sergeantd83/OT-Thing/Firmware/src/portal.cpp

#include <WiFi.h>
#include <Update.h>
#include <ArduinoJson.h>
#include <AsyncTCP.h>
#include <ESPAsyncWebServer.h>
#include <WiFi.h>
#include "portal.h"
#include "devstatus.h"
#include "devconfig.h"
#include "html.h"
#include "otcontrol.h"
#include "otvalues.h"
#include "httpUpdate.h"

static const char APP_JSON[] PROGMEM = "application/json";
#ifdef NODO
const IPAddress apAddress(4, 3, 2, 1);
const IPAddress apMask(255, 255, 255, 0);
#else
static const IPAddress apAddress(4, 3, 2, 1);
static const IPAddress apMask(255, 255, 255, 0);
#endif
Portal portal;
static AsyncWebServer websrv(80);
AsyncWebSocket ws("/ws");


Portal::Portal():
    reboot(false),
    updateEnable(true) {
}

void Portal::begin(bool configMode) {
    if (configMode) {
        WiFi.persistent(false);
#ifdef NODO
        WiFi.disconnect();
        WiFi.mode(WIFI_AP);   // Force AP only so DHCP works reliably
#endif
        WiFi.softAPConfig(apAddress, apAddress, apMask);
#ifdef NODO
        delay(200); // allow stack to settle
        if (!WiFi.softAP(F(AP_SSID), F(AP_PASSWORD))) 
            Serial.println("Failed to start AP"); // print message if setup fails
        else
            Serial.println("AP started successfully");
#else
        WiFi.softAP(F(AP_SSID), F(AP_PASSWORD));

        if (WiFi.SSID().isEmpty())
            WiFi.mode(WIFI_AP);
        else
            WiFi.mode(WIFI_AP_STA);
#endif
        WiFi.setAutoReconnect(false);
#ifndef NODO
        WiFi.persistent(true);
#endif
    }

    websrv.begin();
    websrv.addHandler(&ws);

    websrv.on("/", HTTP_ANY, [](AsyncWebServerRequest *request) {
        #ifdef DEBUG
        if (LittleFS.exists(F("/index.html"))) {
            request->send(LittleFS, F("/index.html"), F("text/html"));
            return;
        }
        #endif
        request->send(200, F("text/html"), (uint8_t*) html, strlen_P(html));
    });

    websrv.on(PSTR("/config"), HTTP_GET, [this] (AsyncWebServerRequest *request) {
        if (LittleFS.exists(FPSTR(CFG_FILENAME)))
            request->send(LittleFS, FPSTR(CFG_FILENAME), FPSTR(APP_JSON));
        else
            request->send(404);
    });

    websrv.on(PSTR("/config"), HTTP_POST, 
        [this] (AsyncWebServerRequest *request) {
        },
        [] (AsyncWebServerRequest *request, const String &filename, size_t index, uint8_t *data, size_t len, bool final) {
        },
        [this] (AsyncWebServerRequest *request, uint8_t *data, size_t len, size_t index, size_t total) {
            static String confBuf;
            if (!index)
                confBuf.clear();

            confBuf.concat((const char*) data, len);

            if (confBuf.length() == total) {
                devconfig.write(confBuf);
                confBuf.clear();
                request->send(200);
            }
        }
    );

    websrv.on(PSTR("/scan"), HTTP_GET, [this] (AsyncWebServerRequest *request) {
        JsonDocument doc;
        JsonObject jobj = doc.to<JsonObject>();

        int n = WiFi.scanComplete();
        jobj[F("status")] = n;
        if (n == -2)
            WiFi.scanNetworks(true);
        else
            if (n >= 0) {
                JsonArray results = jobj[F("results")].to<JsonArray>();
                for (int i=0; i<n; i++) {
                    JsonObject result = results.add<JsonObject>();
                    result[F("ssid")] = WiFi.SSID(i);
                    result[F("rssi")] = WiFi.RSSI(i);
                    result[F("channel")] = WiFi.channel(i);
                }
                WiFi.scanDelete();
            }

        AsyncResponseStream *response = request->beginResponseStream(FPSTR(APP_JSON));
        serializeJson(doc, *response);
        request->send(response);
    });

    websrv.on(PSTR("/setwifi"), HTTP_POST, [this] (AsyncWebServerRequest *request) {
        if (request->hasArg(F("ssid")) && request->hasArg(F("pass"))) {
#ifndef NODO
            request->send(200);
            delay(500);
#endif
            WiFi.disconnect();
            WiFi.persistent(true);
            WiFi.setAutoReconnect(true);
            String ssid = request->arg(F("ssid"));
            String pass = request->arg(F("pass"));
            WiFi.begin(ssid, pass);
#ifdef NODO
            // Trigger the reboot flag handled in Portal::loop()
            this->reboot = true;
            request->send(200, "text/plain", "Credentials Saved. Rebooting...");
#endif
        }
        else
            request->send(400); // bad request
    });

    websrv.on(PSTR("/status"), HTTP_GET, [this](AsyncWebServerRequest *request) {
        if (httpupdate.isUpdating()) {
            request->send(503);
            return;
        }
        JsonDocument doc;
        devstatus.buildDoc(doc);
        AsyncResponseStream *response = request->beginResponseStream(FPSTR(APP_JSON));
        serializeJson(doc, *response);
        request->send(response);
    });

    websrv.on(PSTR("/otitems"), HTTP_GET, [this](AsyncWebServerRequest *request) {
        if (httpupdate.isUpdating()) {
            request->send(503);
            return;
        }
        JsonDocument doc;
        JsonObject jSlave = doc[F("slave")].to<JsonObject>();
            for (auto *valobj: slaveValues)
                valobj->getStatus(jSlave);

        JsonObject jMaster = doc[F("master")].to<JsonObject>();
            for (auto *valobj: thermostatValues)
                valobj->getStatus(jMaster);

        AsyncResponseStream *response = request->beginResponseStream(FPSTR(APP_JSON));
        serializeJson(doc, *response);
        request->send(response);
    });

    websrv.on(PSTR("/reboot"), HTTP_GET, [this](AsyncWebServerRequest *request) {
        request->send(200);
        this->reboot = true;
    });

    websrv.on(PSTR("/update"), HTTP_POST, 
        [this] (AsyncWebServerRequest *request) { // onRequest handler
            int httpRes;

            if (!this->updateEnable || httpupdate.isUpdating()) {
                httpRes = 503; // service unavailable
            }
            else {
                this->reboot = !Update.hasError();
                if (this->reboot)
                    httpRes = 200;
                else
                httpRes = 500;
            }
            AsyncWebServerResponse *response = request->beginResponse(httpRes);
            response->addHeader(F("Connection"), F("close"));
            request->send(response);
        },
        [this] (AsyncWebServerRequest *request, const String &filename, size_t index, uint8_t *data, size_t len, bool final) { // onUpdate handler
            if (!this->updateEnable || httpupdate.isUpdating())
                return;

            if (!index)
                Update.begin(UPDATE_SIZE_UNKNOWN, U_FLASH);

            Update.write(data, len);

            if (final)
                Update.end(true);
        }
    );

    websrv.on(PSTR("/slaverequest"), HTTP_GET, [this](AsyncWebServerRequest *request) {
        if (!request->hasParam("id")) {
            request->send(503);
            return;
        }
        if (!request->hasParam("rw")) {
            request->send(503);
            return;
        }

        SlaveRequestStruct srs;
        srs.idReq = (OpenThermMessageID) request->getParam("id")->value().toInt();
        srs.typeReq = (request->getParam("rw")->value().toInt() != 0) ? OpenThermMessageType::READ_DATA : OpenThermMessageType::WRITE_DATA;

        if (!request->hasParam("data")) {
            request->send(503);
            return;
        }
        String hexData = request->getParam("data")->value();
        srs.dataReq = strtol(hexData.c_str(), nullptr, 16);

        if (otcontrol.slaveRequest(srs)) {    
            JsonDocument doc;
            JsonObject jobj = doc.to<JsonObject>();
            
            jobj["type"] = (int) srs.typeResp;
            jobj["id"] = (int) srs.idReq;
            jobj["data"] = String(OpenTherm::getUInt(srs.dataResp), 16);
            AsyncResponseStream *response = request->beginResponseStream(FPSTR(APP_JSON));
            serializeJson(doc, *response);
            request->send(response);
        }
        else
            request->send(503);
    });

    websrv.on(PSTR("/checkupdate"), HTTP_POST, [this](AsyncWebServerRequest *request) {
        this->checkUpdate = true;
        request->send(200);
    });

    websrv.on(PSTR("/install"), HTTP_POST, [this](AsyncWebServerRequest *request) {
        this->doUpdate = true;
        request->send(200);
    });

    websrv.on(PSTR("/topics"), HTTP_GET, [this](AsyncWebServerRequest *request) {
        String list;
        for (uint8_t topic = Mqtt::TOPIC_OUTSIDETEMP; topic < Mqtt::TOPIC_UNKNOWN; topic++) {
            String line;
            line = mqtt.getCmdTopic((Mqtt::MqttTopic) topic);
            list += line + F("\r\n");
        }
        request->send(200, F("text/plain"), list);
    });
}

void Portal::loop() {
    if (reboot) {
        delay(500);
        ESP.restart();
    }

    if (checkUpdate) {
        checkUpdate = false;
        httpupdate.checkUpdate();
    }

    if (doUpdate) {
        doUpdate = false;
        httpupdate.update();
    }

    ws.cleanupClients();
}

void Portal::textAll(String text) {
    ws.textAll(text);
}
