sergeantd83/OT-Thing/Firmware/src/devconfig.cpp

#include <Arduino.h>
#include <WiFi.h>
#include <ESPmDNS.h>
#include "devconfig.h"
#include "mqtt.h"
#include "otcontrol.h"
#include "sensors.h"
#include <HADiscovery.h>

const char CFG_FILENAME[] PROGMEM = "/config.json";

DevConfig devconfig;
extern bool configMode;

DevConfig::DevConfig():
        writeBufFlag(false),
        fsOk(false) {
}

void DevConfig::begin() {
    fsOk = LittleFS.begin(false);
#ifdef NODO
    if (!fsOk) {
#else
    if (!fsOk || configMode) {
#endif
        if (configMode)
            Serial.println("Config mode: formatting LittleFS and reloading config.");
        else
            Serial.println("LittleFS mount failed; formatting...");

        LittleFS.format();
        fsOk = LittleFS.begin(false);
    }

    if (fsOk)
        Serial.printf("LittleFS mounted: total=%u used=%u\n", (unsigned) LittleFS.totalBytes(), (unsigned) LittleFS.usedBytes());
    else
        Serial.println("LittleFS mount failed; running without persisted config.");
    update();
}

void DevConfig::update() {
    if (!fsOk)
        return;
    File f = getFile();
    if (f) {
        JsonDocument doc;
        deserializeJson(doc, f);

        if (doc[F("hostname")].is<String>())
            hostname = doc[F("hostname")].as<String>();

        if (doc[F("haPrefix")].is<String>())
            HADiscovery::setHAPrefix(doc[F("haPrefix")].as<String>());

        if (doc[F("haName")].is<String>())
            HADiscovery::devName = doc[F("haName")].as<String>();

        timezone = doc[F("timezone")] | 3600;

        if (hostname.isEmpty())
            hostname = F(HOSTNAME);

        if (WiFi.isConnected()) {
            WiFi.setHostname(hostname.c_str());
            MDNS.begin(hostname);
        }

        if (doc[F("mqtt")].is<JsonObject>()) {
            MqttConfig mc;
            const JsonObject &jobj = doc["mqtt"].as<JsonObject>();
            mc.host = jobj["host"].as<String>();
            mc.port = jobj["port"].as<uint16_t>();
            mc.tls = jobj["tls"].as<bool>();
            mc.user = jobj["user"].as<String>();
            mc.pass = jobj["pass"].as<String>();
            mc.keepAlive = jobj["keepAlive"] | 15;
            mqtt.setConfig(mc);
        }

        if (doc[F("outsideTemp")].is<JsonObject>()) {
            JsonObject obj = doc[F("outsideTemp")];
            outsideTemp.setConfig(obj);
        }

        for (int i=0; i<2; i++) {
            JsonObject obj = doc[F("heating")][i][F("roomtemp")];
            roomTemp[i].setConfig(obj);

            JsonObject obj2 = doc[F("heating")][i][F("roomsetpoint")];
            roomSetPoint[i].setConfig(obj2);
        }

        JsonObject cfg = doc.as<JsonObject>();
        otcontrol.setConfig(cfg);

        f.close();
    }
}

File DevConfig::getFile() {
    if (!fsOk)
        return File();
    return LittleFS.open(FPSTR(CFG_FILENAME), "r");
}

void DevConfig::write(String &str) {
    File f = LittleFS.open(FPSTR(CFG_FILENAME), "w");
    f.write((uint8_t *) str.c_str(), str.length());
    f.close();
    writeBufFlag = true;
}

void DevConfig::remove() {
    if (fsOk)
        LittleFS.remove(FPSTR(CFG_FILENAME));
}

void DevConfig::loop() {
    if (fsOk && writeBufFlag) {
        writeBufFlag = false;
        update();
    }
}

String DevConfig::getHostname() const {
    return hostname;
}

int DevConfig::getTimezone() const {
    return timezone;
}
