sergeantd83/OT-Thing/Firmware/src/devstatus.cpp

#include "devstatus.h"
#include <WiFi.h>
#include <rom/rtc.h>
#include "mqtt.h"
#include "otcontrol.h"
#include "sensors.h"
#include "httpUpdate.h"
#include <NimBLEDevice.h>
#ifdef NODO
#include <EthernetESP32.h>
#endif
DevStatus devstatus;

class DevStatusLock: public SemHelper {
public:
    DevStatusLock(): SemHelper(devstatus.mutex, 100) {
    }
};

DevStatus::DevStatus():
        numWifiDiscon(0) {
    mutex = xSemaphoreCreateMutex();
}

bool DevStatus::lock() {
    const auto res = xSemaphoreTake(mutex, (TickType_t) 500 / portTICK_PERIOD_MS);
    return (res == pdTRUE);
}

void DevStatus::unlock() {
    xSemaphoreGive(mutex);
}

 void DevStatus::buildDoc(JsonDocument &doc) {
    doc.clear();
    doc[F("runtime")] = millis() / 1000UL;
    doc[F("freeHeap")] = ESP.getFreeHeap();
    doc[F("largestBlock")] = heap_caps_get_largest_free_block(MALLOC_CAP_8BIT);
    doc[F("resetInfo")] = rtc_get_reset_reason(0);
    doc[F("fw_version")] = F(BUILD_VERSION);
    doc[F("USB_connected")] = Serial.isConnected();
    doc[F("reset_reason0")] = rtc_get_reset_reason(0);
    doc[F("numWifiDisc")] = numWifiDiscon;

    String newFw;
    if (httpupdate.getNewFw(newFw))
        doc[F("new_fw")] = newFw;

    struct tm timeinfo;
    if (getLocalTime(&timeinfo, 0)) {
        char buffer[64];
        strftime(buffer, sizeof(buffer), "%d.%m.%Y %H:%M:%S", &timeinfo);
        doc[F("dateTime")] = buffer;
    }

    JsonObject jwifi = doc[F("wifi")].to<JsonObject>();
    jwifi[F("status")] =  WiFi.status();
    jwifi[F("mode")] = WiFi.getMode();
    jwifi[F("ipsta")] = WiFi.localIP().toString();
    jwifi[F("mac")] = WiFi.macAddress();
    jwifi[F("hostname")] = WiFi.getHostname();
    jwifi[F("sta_ssid")] = WiFi.SSID();
    jwifi[F("rssi")] = WiFi.RSSI();
#ifdef NODO
    if (WIRED_ETHERNET_PRESENT) {
        jwifi[F("sta_ssid")] = "WIRED";
        jwifi[F("ipsta")] = Ethernet.localIP().toString();
    } 
#endif
    JsonObject jmqtt = doc[F("mqtt")].to<JsonObject>();
    jmqtt[F("connected")] = mqtt.connected();
    jmqtt[F("basetopic")] = mqtt.getBaseTopic();
    jmqtt[F("numDisc")] = mqtt.getNumDisc();

    JsonObject jot = doc.as<JsonObject>();
    otcontrol.getJson(jot);

    double outT;
    if (outsideTemp.get(outT))
        doc[F("outsideTemp")] = outT;

    if (!outsideTemp.owResult.isEmpty())
        doc[F("owResult")] = outsideTemp.owResult;
#ifdef NODO
    if (WiFi.getMode() != WIFI_AP && WiFi.getMode() != WIFI_AP_STA) { /* don't do this if in config mode*/
#endif
    JsonObject jo = doc[F("1wire")].to<JsonObject>();
    OneWireNode::writeJsonAll(jo);

    JsonObject ble = doc[F("BLE")].to<JsonObject>();
    BLESensor::writeJsonAll(ble);
#ifdef NODO
    }
#endif
}
