sergeantd83/OT-Thing/Firmware/include/HADiscLocal.h

#pragma once
#include "HADiscovery.h"
#include "mqtt.h"

class OTThingHADiscovery: public HADiscovery {
public:
    OTThingHADiscovery();
    void begin();
    void createSwitch(String name, Mqtt::MqttTopic topic);
    using HADiscovery::publish;
    bool publish(const bool avail = true);
};

extern OTThingHADiscovery haDisc;
